Prateek7805/key_chain_led_matrix/ASCII_Table.h

uint8_t ASCIIArray[][8] = {{0,0,0,0,0,0,0,0},
{0,0,0,223,223,0,0,0},
{7,0,7,0,0,0,0,0},
{102,255,255,102,102,255,255,102},
{0,4,42,42,127,42,42,16},
{198,105,54,24,108,150,99,0},
{56,100,100,254,253,101,98,0},
{0,0,7,23,15,0,0,0},
{0,0,0,0,60,126,195,129},
{129,195,126,60,0,0,0,0},
{8,42,28,127,28,42,8,0},
{0,24,24,126,126,24,24,0},
{0,0,152,248,120,0,0,0},
{0,0,24,24,24,0,0,0},
{0,0,224,224,224,0,0,0},
{192,96,48,24,12,6,3,0},
{0,126,255,195,195,255,126,0},
{0,192,198,255,255,192,192,0},
{0,198,227,243,243,223,206,0},
{0,102,231,195,219,255,102,0},
{0,56,60,54,243,241,48,0},
{0,207,223,219,219,251,115,0},
{0,126,223,219,219,251,112,0},
{0,3,3,243,251,15,7,0},
{0,118,223,219,219,255,118,0},
{0,14,31,27,27,255,254,0},
{0,0,231,231,231,0,0,0},
{96,123,59,0,0,0,0,0},
{0,24,60,102,195,0,0,0},
{0,108,108,108,108,108,0,0},
{0,195,102,60,24,0,0,0},
{0,6,7,179,187,15,6,0},
{126,129,153,165,189,161,158,64},
{254, 255, 51, 51, 51, 51, 255, 254},
{255, 255, 219, 219, 219, 255, 126, 38},
{126,255,195,195,195,195,195,195},
{255, 255, 195, 195, 195, 231, 126, 60},
{255, 255, 219, 219, 219, 219, 219, 0},
{255, 255, 27, 27, 27, 27, 27, 0},
{126, 255, 195, 195, 219, 219, 251, 122},
{255, 255, 24, 24, 24, 24, 255, 255},
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
